architolk/fm-synth/media/EFX-AM.jpg

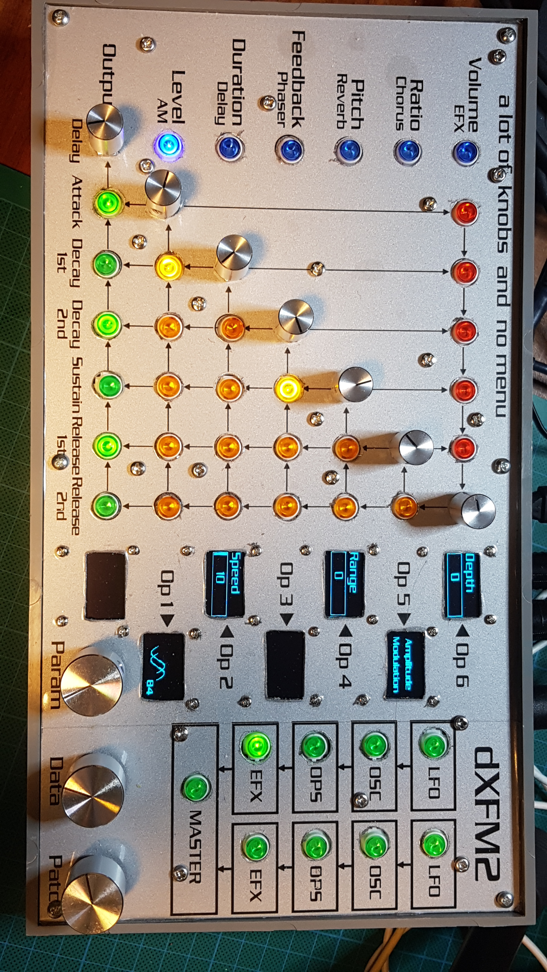
media/EFX-AM.jpg
