architolk/fm-synth/media/EFX-AM.png

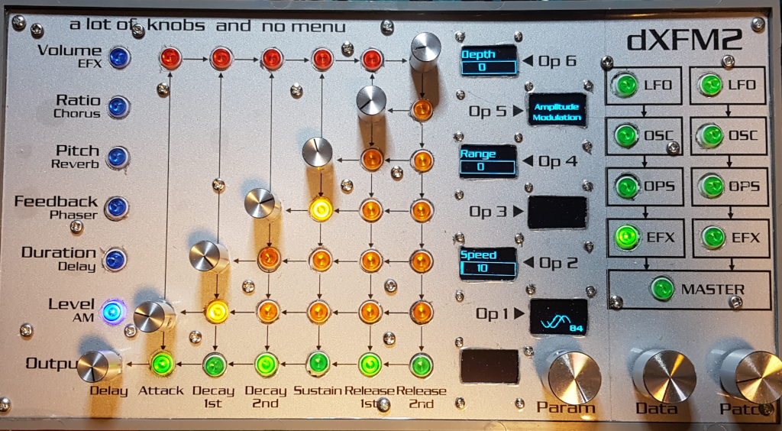
media/EFX-AM.png
