architolk/fm-synth/media/EFX-Chorus.png

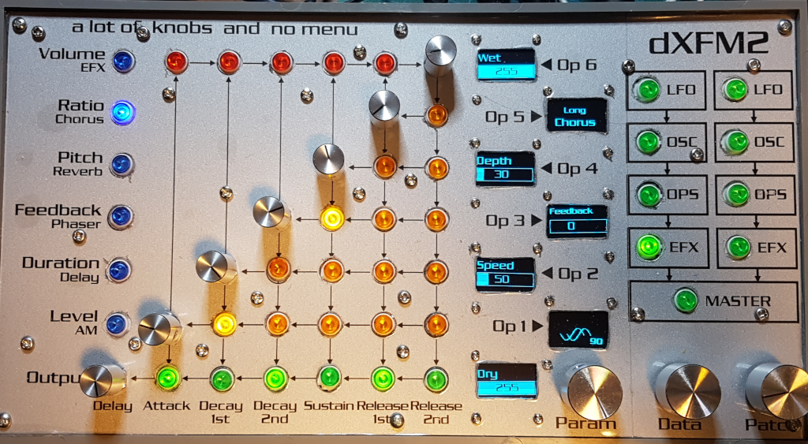
media/EFX-Chorus.png
