architolk/fm-synth/media/EFX-Reverb.jpg

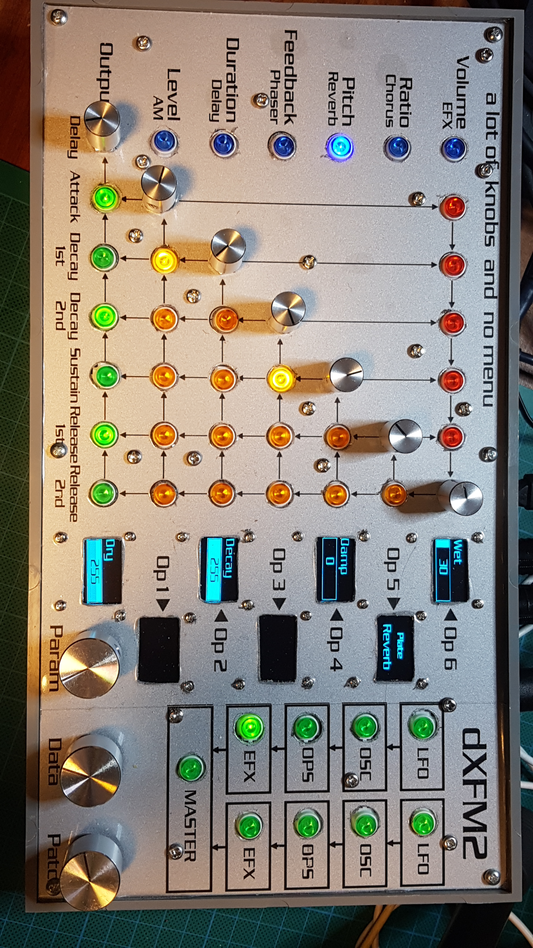
media/EFX-Reverb.jpg
