architolk/fm-synth/media/EFX.png

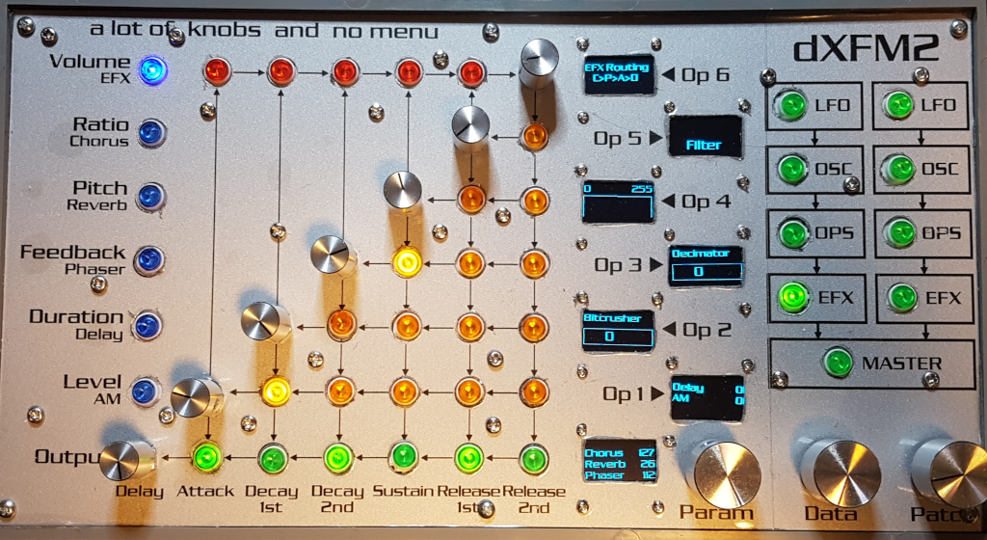
media/EFX.png
