architolk/fm-synth/media/LFO-Duration.png

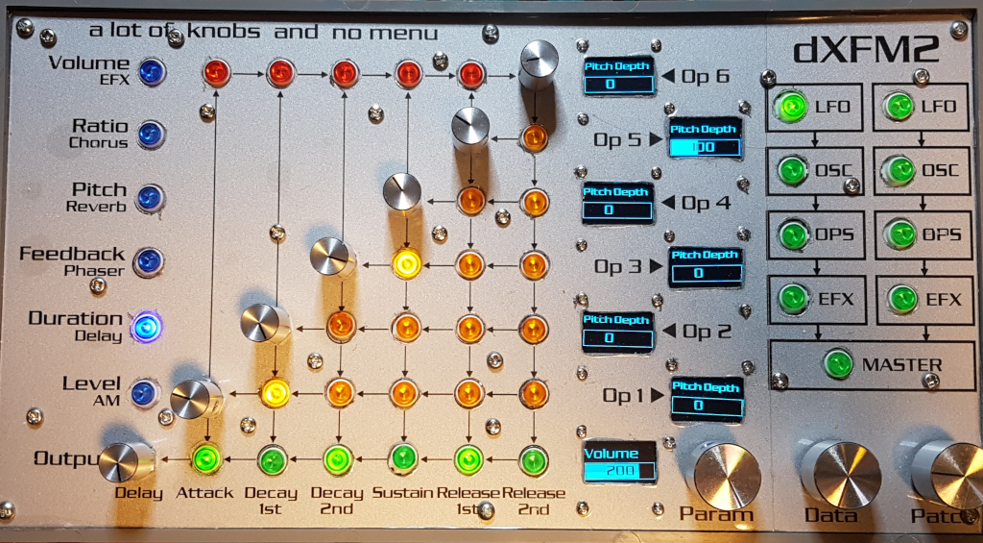
media/LFO-Duration.png
