architolk/fm-synth/media/LFO-Level.png

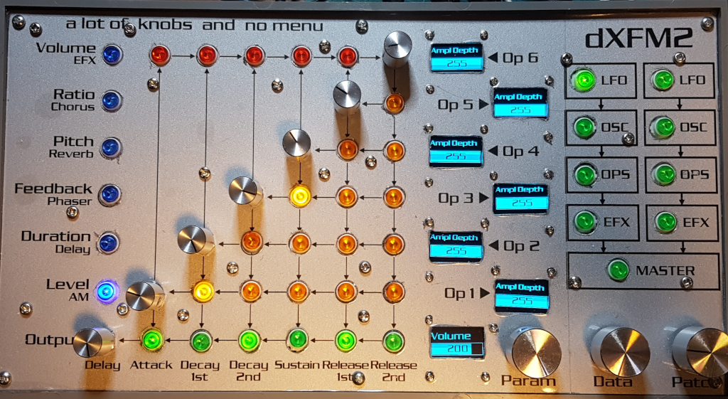
media/LFO-Level.png
