architolk/fm-synth/media/MASTER-Volume.png

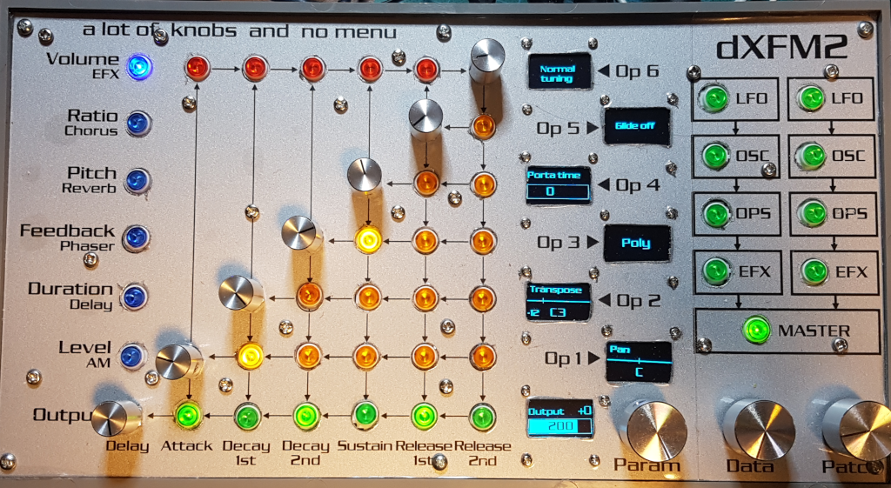
media/MASTER-Volume.png
