architolk/fm-synth/media/MENU-Algorithm.png

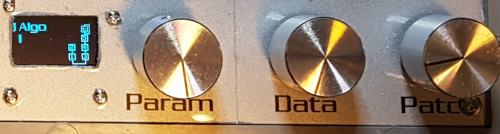
media/MENU-Algorithm.png
