architolk/fm-synth/media/MENU-Init.png

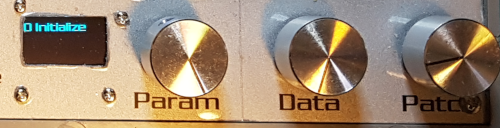
media/MENU-Init.png
