architolk/fm-synth/media/OPS-Level.png

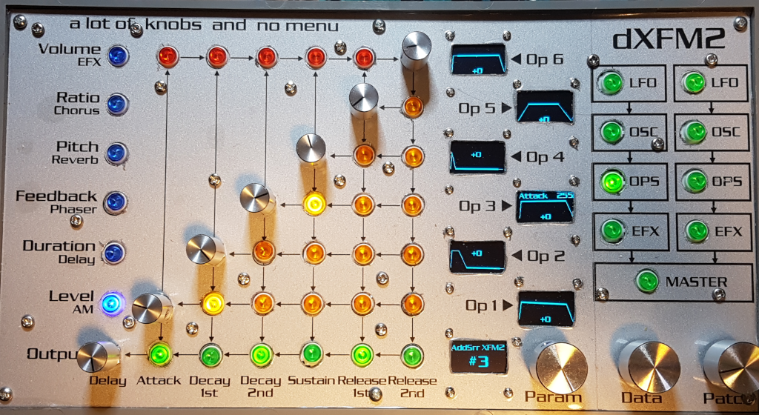
media/OPS-Level.png
