architolk/fm-synth/media/OPS-Ratio.jpg

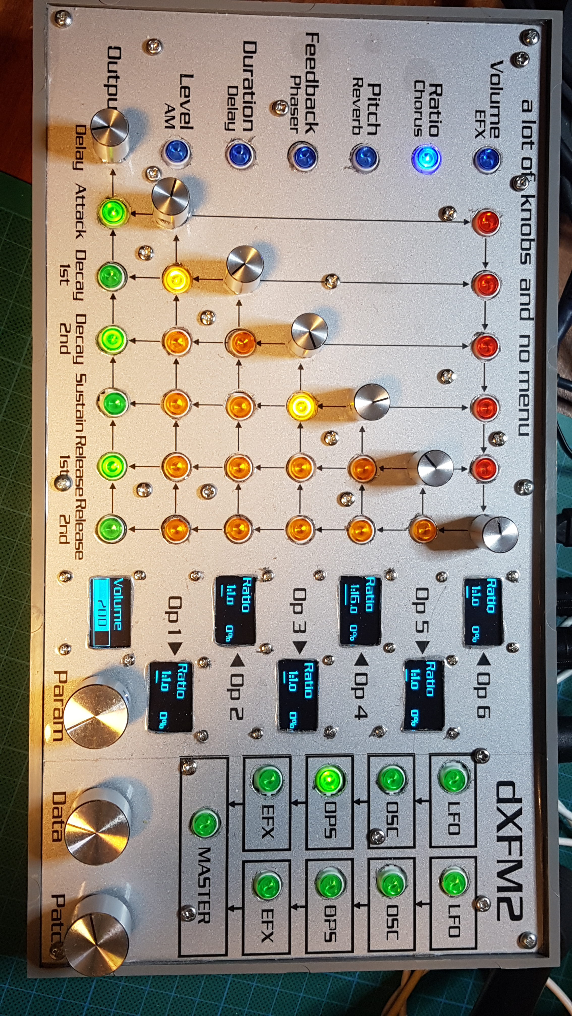
media/OPS-Ratio.jpg
