architolk/fm-synth/media/OPS-Ratio.png

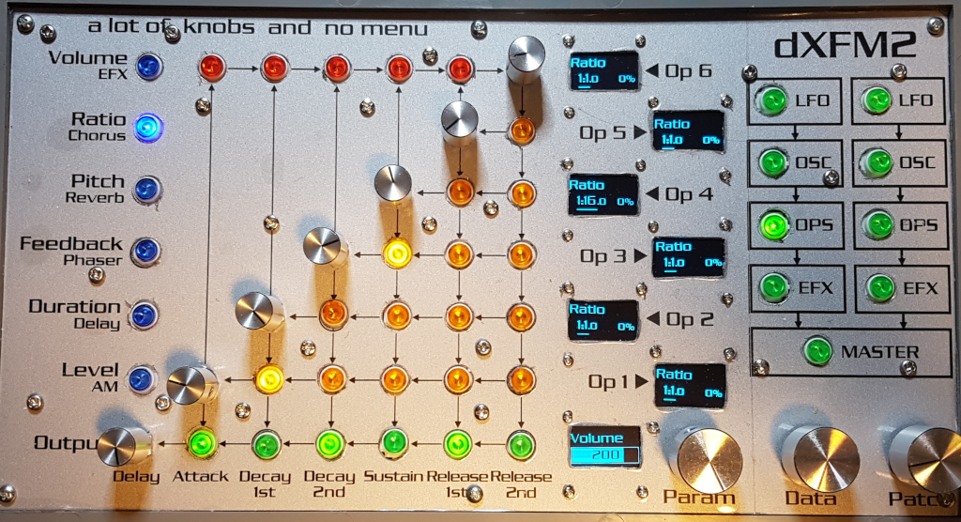
media/OPS-Ratio.png
