architolk/fm-synth/media/OSC-Envelope.png

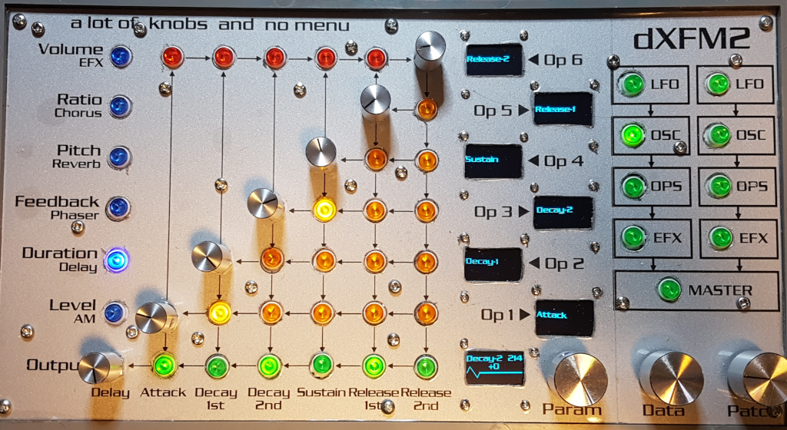
media/OSC-Envelope.png
