architolk/fm-synth/media/OSC-Pitch.png

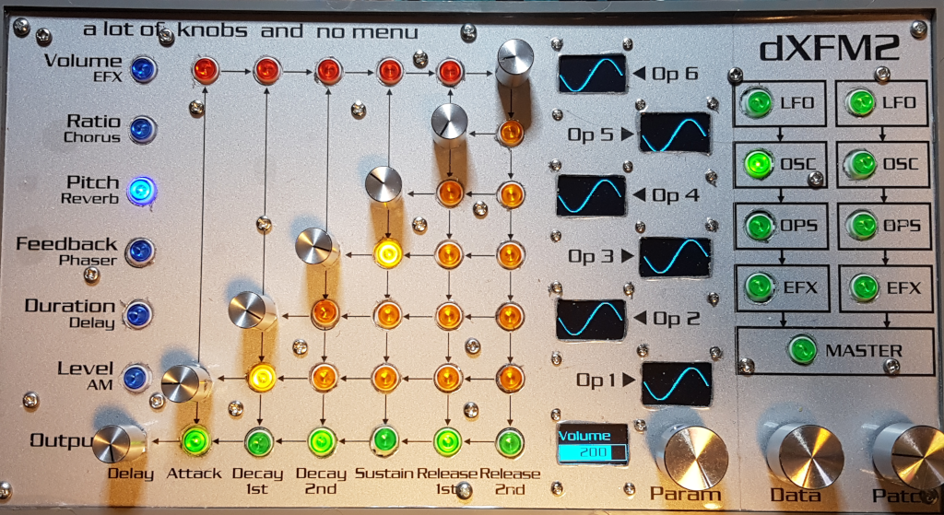
media/OSC-Pitch.png
