architolk/fm-synth/media/OSC-Ratio.png

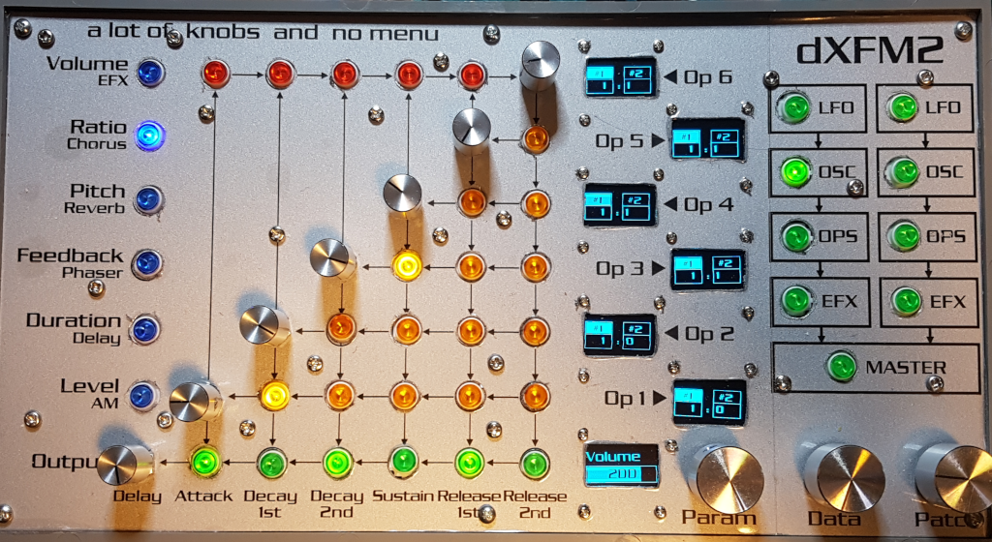
media/OSC-Ratio.png
