architolk/fm-synth/src/dXFM2/Waves.ino

/*
*  Module for the waves
*
*  this module is about storing the wavesforms that can be displayed
*
*/

//Data is structured as a sample value range -127 to 127

//Wave forms for the synth, created with the WCreate utility
//0 = Sine wave: "(x=1)"
//1 = Triangle wave with one odd partical: "(x=1)*0.8-(x=3)/9" (0.8 for better display, a 1.0 first harmonic would be more correct)
//2 = Triangle wave with two odd particals: "(x=1)-(x=3)/9+(x=5)/25"
//3 = Triangle wave without the 3th harmonic, upto the 13th odd harmonic: "(x=1)+(x=5)/25-(x=7)/49+(x=9)/81-(x=11)/121+(x=13)/169"
//4 = Wave with odd particals: "(x=1)+(x=3)/9-(x=5)/25+(x=7)/49-(x=9)/81+(x=11)/121"
//5 = Wave with odd particals: "(x=1)-(x=3)/9-(x=5)/25+(x=7)/49+(x=9)/81-(x=11)/121"
//6 = First and Third partical, in 3/4 - 1/4 ratio: "(x=1)*0.75-(x=3)*0.25"
//7 = Square wave with odd particals from 1 to 17: "(x=1)+(x=3)/3+(x=5)/5+(x=7)/7+(x=9)/9+(x=11)/11+(x=13)/13+(x=15)/15+(x=17)/17"
//Other waves, for LFO:
//8 = Pure triangle
//9 = Pure square
//10 = Pure saw up
//11 = Pure saw down
//12 = Random
const int8_t WAVES[13][122] PROGMEM = {
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
  showWaveOnScreen(WAVES[LFOMAP[wave]],screen);
}

void displayLRPhase(uint8_t screen, uint8_t lrphase) {
  uint16_t phasediv = lrphase*30;
  phasediv = phasediv/255;
  uint8_t x = 30-phasediv/2;
  drawWave(WAVES[0],x,30,28);
  drawWave(WAVES[0],x+phasediv,30,28);

}
